AGHRapidPro/FFC3/docs/cura/8.2.png

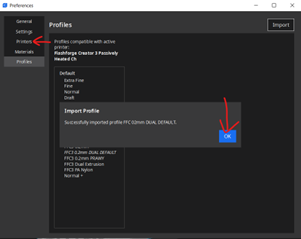
docs/cura/8.2.png
